mri-kisoo/RespiMotionSimulator/Motion Phantom/part (c).STL

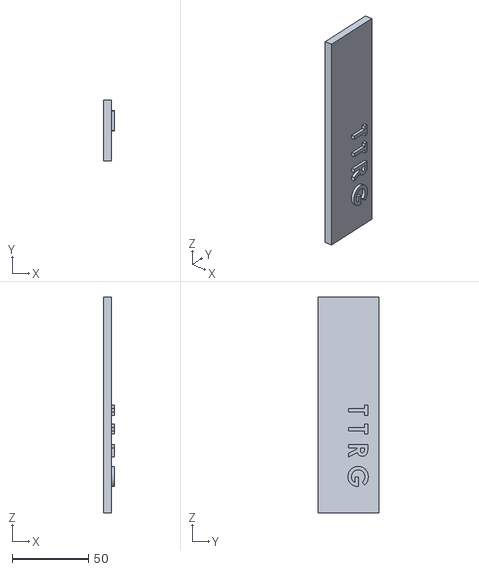
[picture p15: CAD file, 2021-10-23]
Motion Phantom/part (c).STL
7.00 x 40.0 x 142.0
