mri-kisoo/RespiMotionSimulator/Motion Actuator/volume_control_1cm.STL

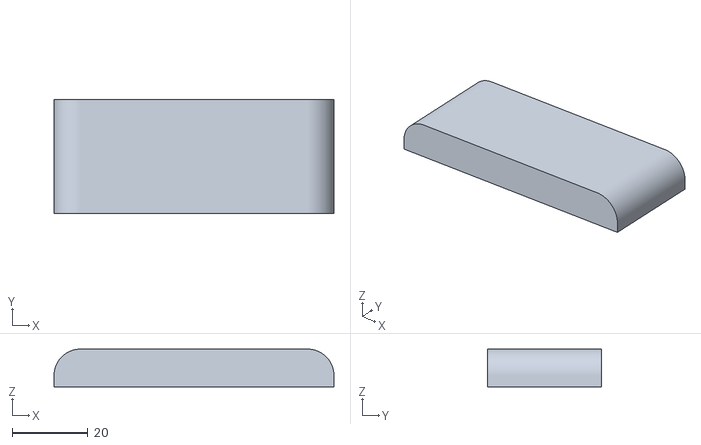
[picture p16: CAD file, 2021-10-23]
Motion Actuator/volume_control_1cm.STL
74.0 x 30.0 x 10.0
