mri-kisoo/RespiMotionSimulator/Motion Actuator/actuator_A.STL

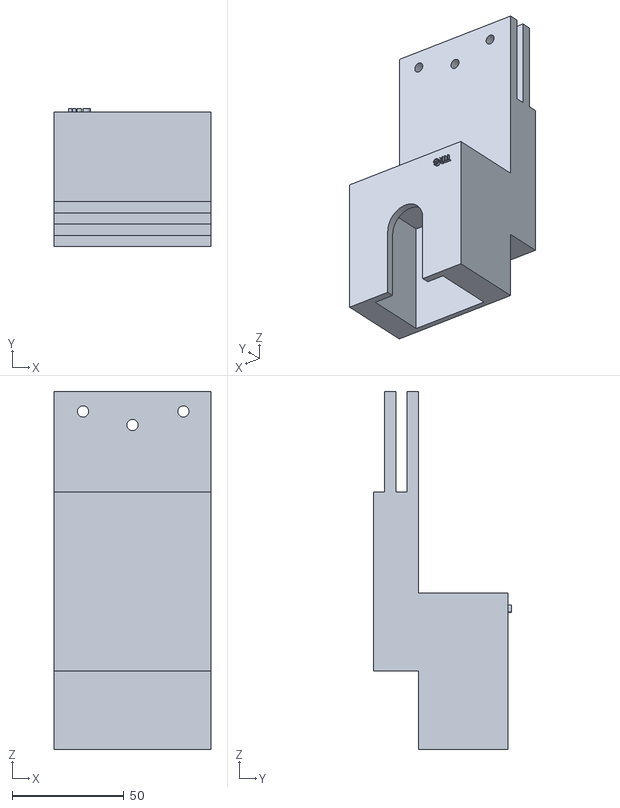
[picture p17: CAD file, 2021-10-23]
Motion Actuator/actuator_A.STL
70.0 x 61.5 x 160.0
