mri-kisoo/RespiMotionSimulator/Motion Actuator/BVM_holder_A.STL

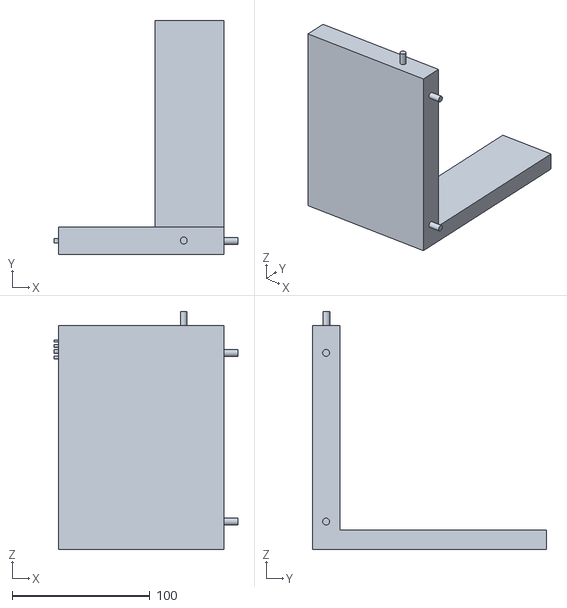
[picture p18: CAD file, 2021-10-23]
Motion Actuator/BVM_holder_A.STL
133.2 x 170.0 x 172.7
