mri-kisoo/RespiMotionSimulator/Motion Actuator/piston_holder_C.STL

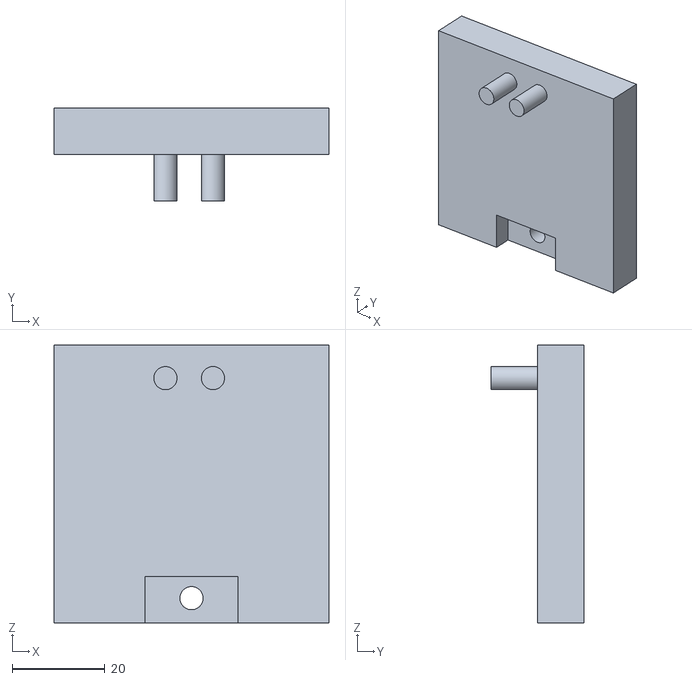
[picture p19: CAD file, 2021-10-23]
Motion Actuator/piston_holder_C.STL
59.4 x 20.0 x 60.0
