mri-kisoo/RespiMotionSimulator/Motion Actuator/ConnectingRod.STL

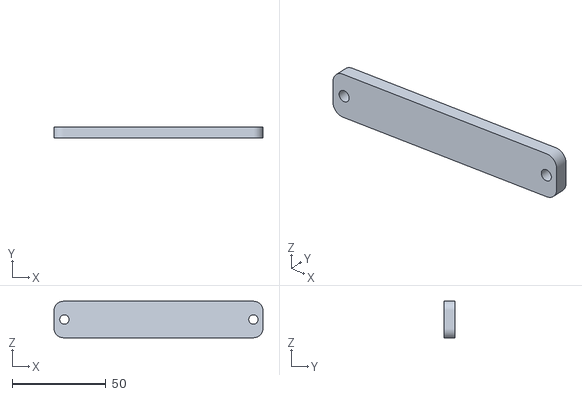
[picture p20: CAD file, 2021-10-23]
Motion Actuator/ConnectingRod.STL
111.6 x 6.00 x 19.5
