mri-kisoo/RespiMotionSimulator/Motion Actuator/volume_control_5mm.STL

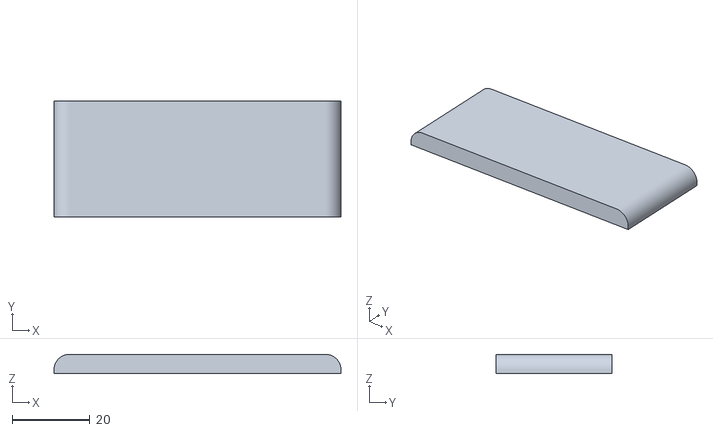
[picture p21: CAD file, 2021-10-23]
Motion Actuator/volume_control_5mm.STL
74.0 x 30.0 x 5.00
