mri-kisoo/RespiMotionSimulator/Motion Actuator/actuator_B.STL

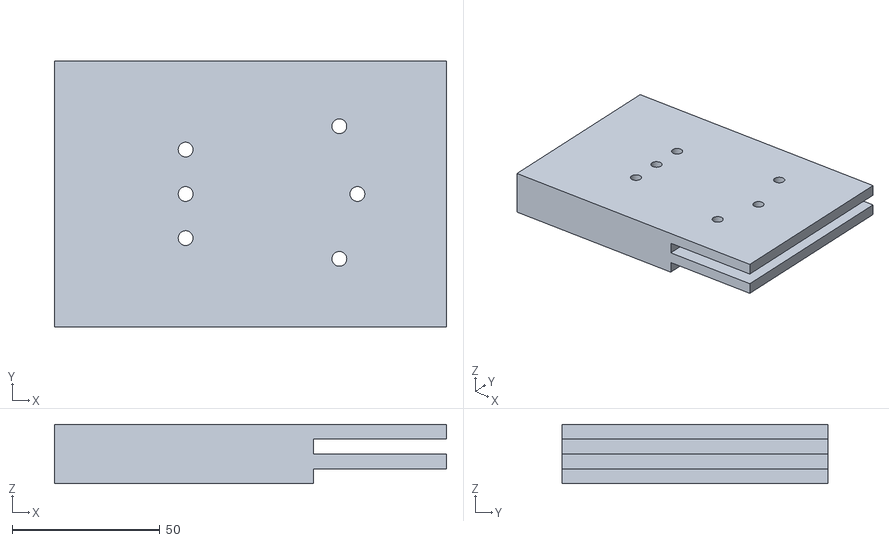
[picture p22: CAD file, 2021-10-23]
Motion Actuator/actuator_B.STL
132.5 x 89.8 x 20.0
