mri-kisoo/RespiMotionSimulator/Motion Actuator/piston_holder_B.STL

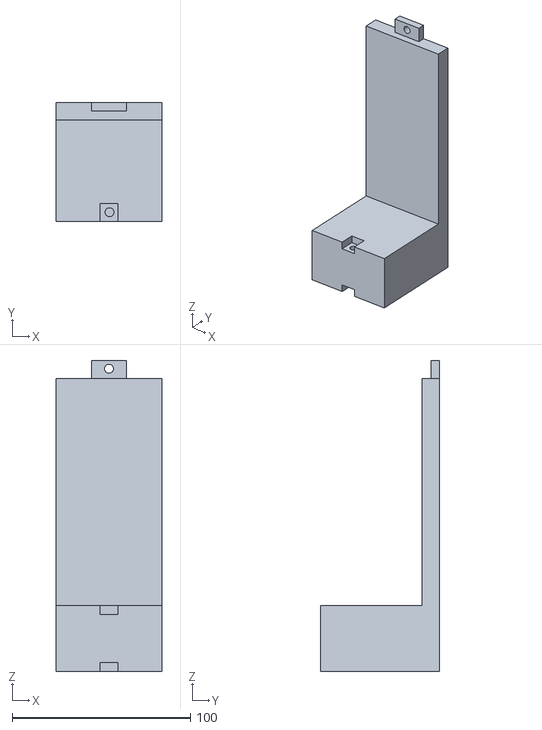
[picture p23: CAD file, 2021-10-23]
Motion Actuator/piston_holder_B.STL
59.4 x 66.9 x 174.4
