mri-kisoo/RespiMotionSimulator/Motion Actuator/Bumper.STL

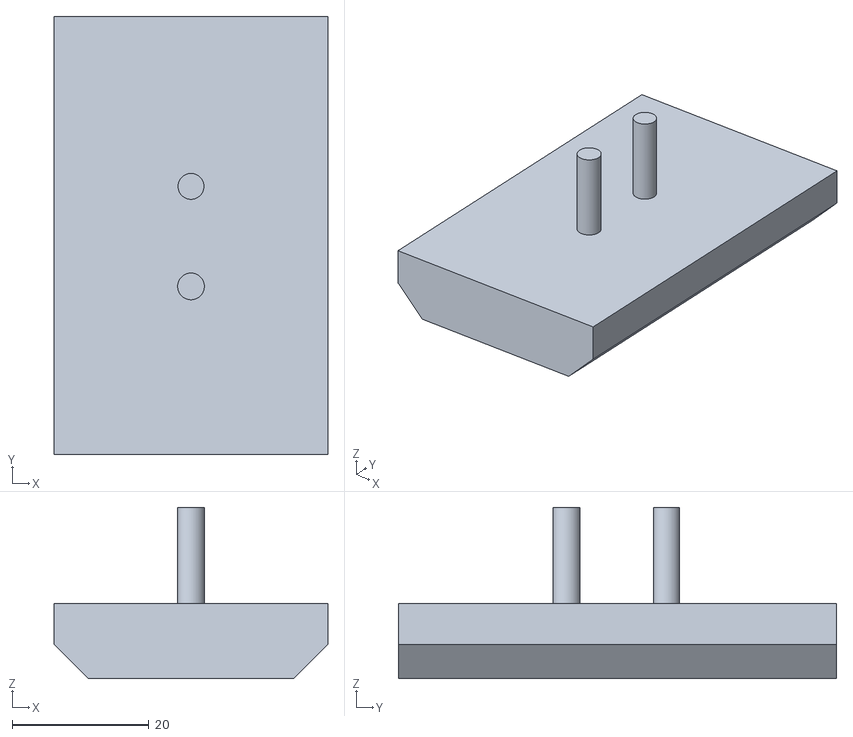
[picture p24: CAD file, 2021-10-23]
Motion Actuator/Bumper.STL
40.0 x 64.0 x 25.0
