mri-kisoo/RespiMotionSimulator/Motion Actuator/BVM_holder_B.STL

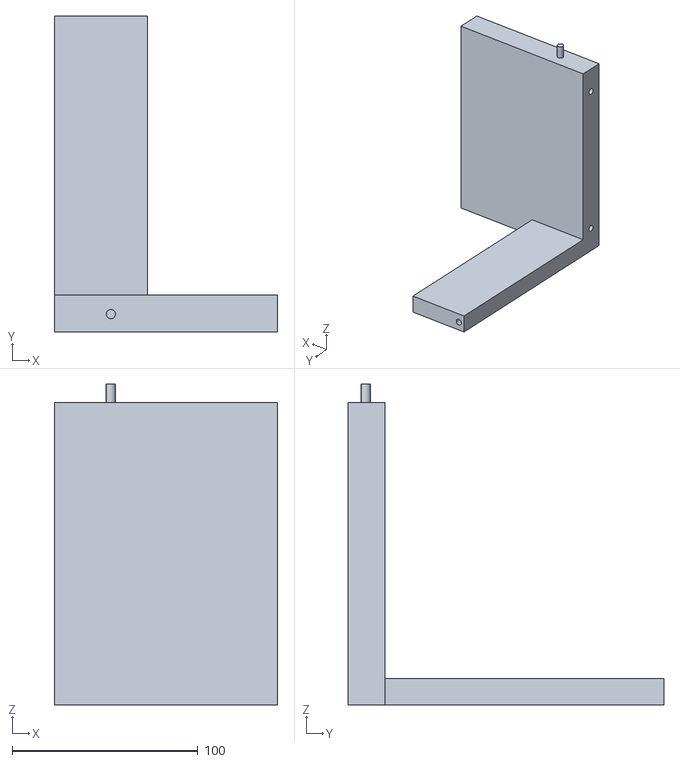
[picture p25: CAD file, 2021-10-23]
Motion Actuator/BVM_holder_B.STL
120.2 x 170.1 x 172.7
